deets/junior-rocket/junior-rocket-state.cpp

// (c) Diez Roggisch, 2023
// SPDX-License-Identifier: MIT


#include "junior-rocket-state.hpp"
#ifdef USE_IOSTREAM
#include <iostream>
#endif

using namespace far::junior;

JuniorRocketState::JuniorRocketState(StateObserver& state_observer)
  : _state_machine(state::IDLE)
  , _state_observer(state_observer)
{
  auto& sm = _state_machine; // Just a convenient alias
  sm.add_transition(state::IDLE, duration_t::zero(), state::ESTABLISH_GROUND_PRESSURE);
  sm.add_transition(state::ESTABLISH_GROUND_PRESSURE, event::GROUND_PRESSURE_ESTABLISHED, state::WAIT_FOR_LAUNCH);
  sm.add_transition(state::WAIT_FOR_LAUNCH, event::ACCELERATION_ABOVE_THRESHOLD, state::ACCELERATION_DETECTED);
  sm.add_transition(state::ACCELERATION_DETECTED, event::ACCELERATION_BELOW_THRESHOLD, state::WAIT_FOR_LAUNCH);
  sm.add_transition(state::ACCELERATION_DETECTED, timeouts::ACCELERATION, state::ACCELERATING);
  sm.add_transition(state::ACCELERATING, event::ACCELERATION_BELOW_THRESHOLD, state::WAIT_FOR_LAUNCH);
  sm.add_transition(state::ACCELERATING, event::PRESSURE_BELOW_LAUNCH_THRESHOLD, state::LAUNCHED);
  sm.add_transition(state::LAUNCHED, event::ACCELERATION_AROUND_ZERO, state::BURNOUT);
  sm.add_transition(state::LAUNCHED, timeouts::MOTOR_BURNTIME - timeouts::ACCELERATION, state::BURNOUT);
  sm.add_transition(state::BURNOUT, timeouts::SEPARATION_TIMEOUT, state::SEPARATION);
  sm.add_transition(state::SEPARATION, duration_t::zero(), state::COASTING);
  sm.add_transition(state::COASTING, event::PRESSURE_PEAK_REACHED, state::FALLING_);
  sm.add_transition(state::COASTING, event::EXPECTED_APOGEE_TIME_REACHED, state::FALLING_);
  sm.add_transition(state::FALLING_, timeouts::FALLING_PRESSURE_TIMEOUT, state::MEASURE_FALLING_PRESSURE1);
  sm.add_transition(state::MEASURE_FALLING_PRESSURE1, timeouts::FALLING_PRESSURE_TIMEOUT, state::MEASURE_FALLING_PRESSURE2);
  sm.add_transition(state::MEASURE_FALLING_PRESSURE2, timeouts::FALLING_PRESSURE_TIMEOUT, state::MEASURE_FALLING_PRESSURE3);
  sm.add_transition(state::MEASURE_FALLING_PRESSURE3, event::PRESSURE_LINEAR, state::DROUGE_OPENED);
  sm.add_transition(state::MEASURE_FALLING_PRESSURE3, event::PRESSURE_QUADRATIC, state::DROUGE_FAILED);
  sm.add_transition(state::DROUGE_OPENED, event::PRESSURE_ABOVE_LAUNCH_THRESHOLD, state::LANDED);
  sm.add_transition(state::DROUGE_FAILED, event::PRESSURE_ABOVE_LAUNCH_THRESHOLD, state::LANDED);
  sm.add_transition(state::DROUGE_FAILED, event::RESTART_PRESSURE_MEASUREMENT, state::FALLING_);
}


std::optional<float> JuniorRocketState::ground_pressure() const
{
  return _ground_pressure;
}

void JuniorRocketState::process_pressure(float pressure)
{
  if(_ground_pressure_stats)
  {
    const auto stats = _ground_pressure_stats->update(pressure);
    if(stats)
    {
      #ifdef USE_IOSTREAM
      std::cout << "pressure stats: " << stats->average << ", " << stats->variance <<  "\n";
      #endif
      if(stats->variance < PRESSURE_VARIANCE_THRESHOLD)
      {
        _ground_pressure = stats->average;
      }
    }
  }
  if(_peak_pressure_stats)
  {
    if(_peak_pressure_stats->update(pressure))
    {
      if(_peak_pressure)
      {
        const auto median = *_peak_pressure_stats->median();
        #ifdef USE_IOSTREAM
        std::cout << "median: " << *_peak_pressure << "\n";
        #endif
        _peak_pressure = std::min(median, *_peak_pressure);
      }
      else
      {
        _peak_pressure = *_peak_pressure_stats->median();
      }
      #ifdef USE_IOSTREAM
      std::cout << "peak pressure: " << *_peak_pressure << "\n";
      #endif
    }
  }
}

void JuniorRocketState::produce_events(timestamp_t timestamp, float pressure, float acceleration)
{
  if(_ground_pressure) {
    feed(timestamp, event::GROUND_PRESSURE_ESTABLISHED);
    if(*_ground_pressure - pressure >= LAUNCH_PRESSURE_DIFFERENTIAL)
    {
      feed(timestamp, event::PRESSURE_BELOW_LAUNCH_THRESHOLD);
    }
    else
    {
      feed(timestamp, event::PRESSURE_ABOVE_LAUNCH_THRESHOLD);
    }
  }

  if(acceleration > LAUNCH_ACCELERATION_THRESHOLD)
  {
    feed(timestamp, event::ACCELERATION_ABOVE_THRESHOLD);
  }
  else
  {
    feed(timestamp, event::ACCELERATION_BELOW_THRESHOLD);
    if(acceleration < FREEFALL_ACCELERATION_THRESHOLD)
    {
      feed(timestamp, event::ACCELERATION_AROUND_ZERO);
    }
  }

  if(_peak_pressure && pressure > *_peak_pressure + PEAK_PRESSURE_MARGIN)
  {
    feed(timestamp, event::PRESSURE_PEAK_REACHED);
  }

  if(flighttime() && *flighttime() >= (APOGEE_TIME + APOGEE_DETECTION_MARGIN))
  {
    feed(timestamp, event::EXPECTED_APOGEE_TIME_REACHED);
  }

  if(_pressure_drop_assessment)
  {
    switch(*_pressure_drop_assessment)
    {
    case pressure_drop::LINEAR:
      feed(timestamp, event::PRESSURE_LINEAR);
      break;
    case pressure_drop::QUADRATIC:
      feed(timestamp, event::PRESSURE_QUADRATIC);
      break;
    }
    // We need to re-measure
    _pressure_drop_assessment = std::nullopt;
  }
}

void JuniorRocketState::feed(timestamp_t timestamp, event e)
{
  _state_machine.feed(e);
  _state_observer.event_produced(timestamp, e);
}

void JuniorRocketState::handle_state_transition(state to, float pressure)
{
  switch(to)
  {
  case state::ESTABLISH_GROUND_PRESSURE:
    // This kicks of the statistics of the ground pressure calibration
    _ground_pressure_stats = decltype(_ground_pressure_stats)::value_type();
    break;
  case state::WAIT_FOR_LAUNCH:
    _liftoff_timestamp = std::nullopt;
    // no need to feed the machine again
    _ground_pressure_stats = std::nullopt;
    break;
  case state::ACCELERATION_DETECTED:
    _liftoff_timestamp = *_last_timestamp;
    break;
  case state::LAUNCHED:
    _peak_pressure_stats = decltype(_peak_pressure_stats)::value_type();
    break;
  case state::FALLING_:
    // We don't need to keep track anymore
    _peak_pressure_stats = std::nullopt;
    break;
  case state::MEASURE_FALLING_PRESSURE1:
    _pressure_measurements[0] = pressure;
    break;
  case state::MEASURE_FALLING_PRESSURE2:
    _pressure_measurements[1] = pressure;
    break;
  case state::MEASURE_FALLING_PRESSURE3:
    _pressure_measurements[2] = pressure;
    assess_pressure_drop();
    break;
  default:
    break;
  }
}

void JuniorRocketState::assess_pressure_drop()
{
  // TOOD: actually implement
  _pressure_drop_assessment = pressure_drop::LINEAR;
}

void JuniorRocketState::drive(timestamp_t timestamp, float pressure, float acceleration)
{
  _state_observer.data(timestamp, pressure, acceleration);
  if(!_last_timestamp)
  {
    _last_timestamp = timestamp;
    // Initial call of state observer for our start-state
    _state_observer.state_changed(timestamp, _state_machine.state());
    return;
  }
  // TODO: timediff!
  const auto elapsed = timestamp - *_last_timestamp;
  _last_timestamp = timestamp;
  process_pressure(pressure);

  const auto old = _state_machine.state();

  // Drive timer events
  _state_machine.elapsed(elapsed);
  _state_observer.elapsed(timestamp, elapsed);

  produce_events(timestamp, pressure, acceleration);

  const auto to = _state_machine.state();
  if(old != to)
  {
    handle_state_transition(to, pressure);
    _state_observer.state_changed(timestamp, to);
  }

}

std::optional<duration_t> JuniorRocketState::flighttime() const
{
  if(_liftoff_timestamp)
  {
    // We know _last_timestamp must be valid, as
    // no liftoff could exist otherwise
    return *_last_timestamp - *_liftoff_timestamp;
  }
  return std::nullopt;
}

#ifdef USE_IOSTREAM
void JuniorRocketState::dot(std::ostream &os)
{
  _state_machine.dot(os, "us");
}
#endif

namespace far::junior {

#ifdef USE_IOSTREAM
#define M_STATE(_state) \
  case state::_state: \
  os << #_state; \
  break;


std::ostream& operator<<(std::ostream& os, const state& state)
{
  switch(state)
  {
    M_STATE(IDLE)
    M_STATE(ESTABLISH_GROUND_PRESSURE)
    M_STATE(WAIT_FOR_LAUNCH)
    M_STATE(ACCELERATION_DETECTED)
    M_STATE(ACCELERATING)
    M_STATE(LAUNCHED)
    M_STATE(BURNOUT)
    M_STATE(SEPARATION)
    M_STATE(COASTING)
    M_STATE(PEAK_REACHED)
    M_STATE(FALLING_)
    M_STATE(MEASURE_FALLING_PRESSURE1)
    M_STATE(MEASURE_FALLING_PRESSURE2)
    M_STATE(MEASURE_FALLING_PRESSURE3)
    M_STATE(DROUGE_OPENED)
    M_STATE(DROUGE_FAILED)
    M_STATE(LANDED);
  }
  return os;
}

#define M_EVENT(_event) \
  case event::_event: \
  os << #_event; \
  break;

std::ostream& operator<<(std::ostream& os, const event& event)
{
  switch(event)
  {
    M_EVENT(GROUND_PRESSURE_ESTABLISHED)
    M_EVENT(PRESSURE_BELOW_LAUNCH_THRESHOLD)
    M_EVENT(PRESSURE_ABOVE_LAUNCH_THRESHOLD)
    M_EVENT(PRESSURE_PEAK_REACHED)
    M_EVENT(ACCELERATION_BELOW_THRESHOLD)
    M_EVENT(ACCELERATION_ABOVE_THRESHOLD)
    M_EVENT(ACCELERATION_AROUND_ZERO)
    M_EVENT(PRESSURE_LINEAR)
    M_EVENT(PRESSURE_QUADRATIC)
    M_EVENT(RESTART_PRESSURE_MEASUREMENT)
    M_EVENT(EXPECTED_APOGEE_TIME_REACHED);
  }
  return os;
}
#endif

} // namespace far::junior

namespace tfa {

std::ostream& operator<<(std::ostream& os, const far::junior::duration_t& d)
{
  using namespace std::chrono_literals;
  os << (d / 1us);
  return os;
}

}
